anthonytec2/OctoSense/OctoSense/CAD/Mock Motherboard.SLDPRT

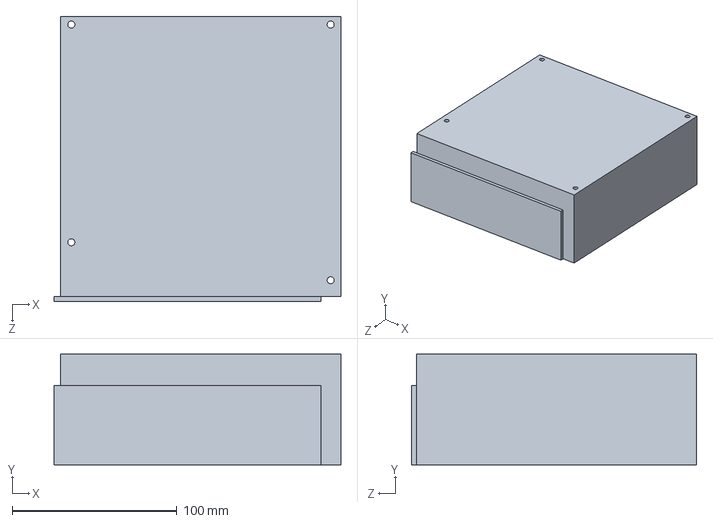
[picture p16: CAD file, 2026-06-25]
OctoSense/CAD/Mock Motherboard.SLDPRT
174.0 x 67.0 x 173.0 mm
