anthonytec2/OctoSense/OctoSense/CAD/Top Camera Case.SLDPRT

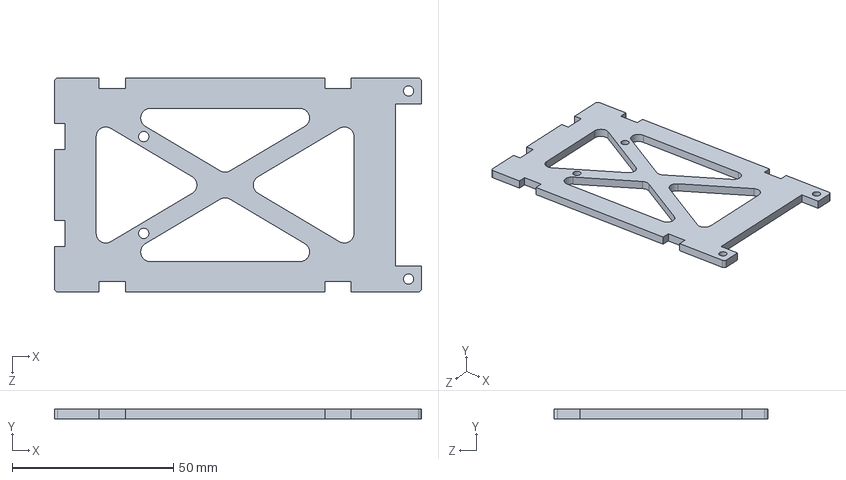
[picture p17: CAD file, 2026-06-25]
OctoSense/CAD/Top Camera Case.SLDPRT
113.8 x 3.17 x 66.3 mm
