anthonytec2/OctoSense/OctoSense/CAD/Mock Battery.SLDPRT

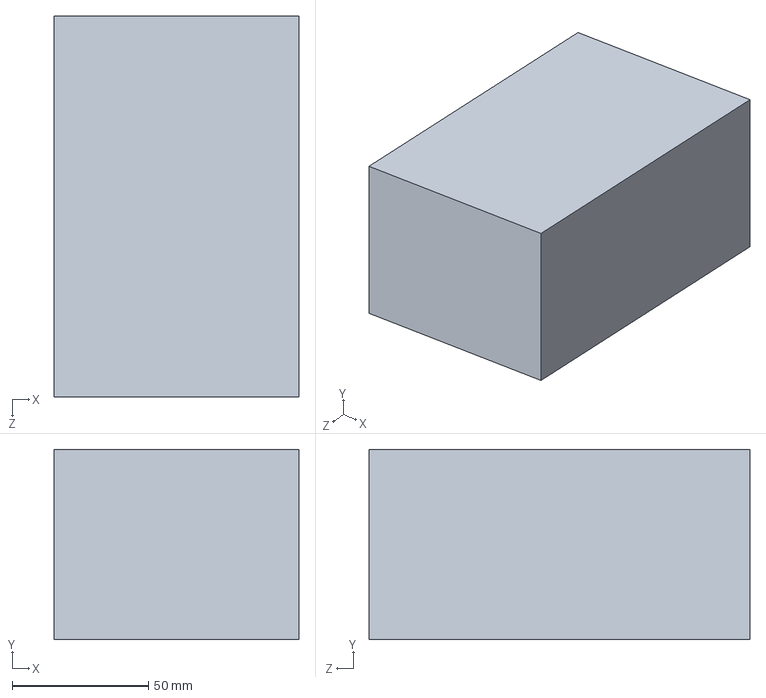
[picture p18: CAD file, 2026-06-25]
OctoSense/CAD/Mock Battery.SLDPRT
90.0 x 70.0 x 140.0 mm
