anthonytec2/OctoSense/OctoSense/CAD/Components Plate.SLDPRT

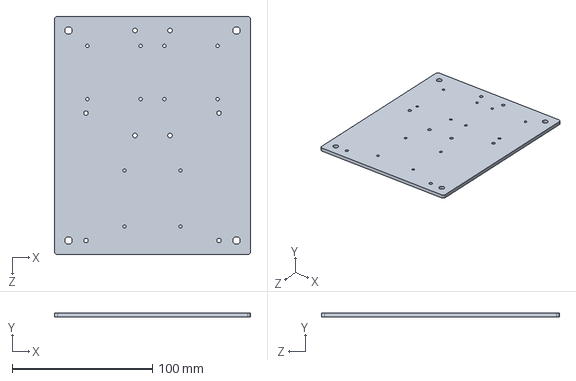
[picture p19: CAD file, 2026-06-25]
OctoSense/CAD/Components Plate.SLDPRT
140.0 x 3.17 x 170.0 mm
