anthonytec2/OctoSense/OctoSense/CAD/Car Mount.SLDPRT

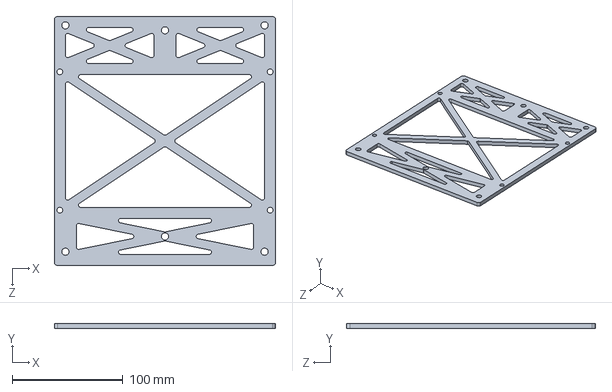
[picture p20: CAD file, 2026-06-25]
OctoSense/CAD/Car Mount.SLDPRT
200.0 x 4.76 x 225.0 mm
