anthonytec2/OctoSense/OctoSense/CAD/Mock Ouster Power.SLDPRT

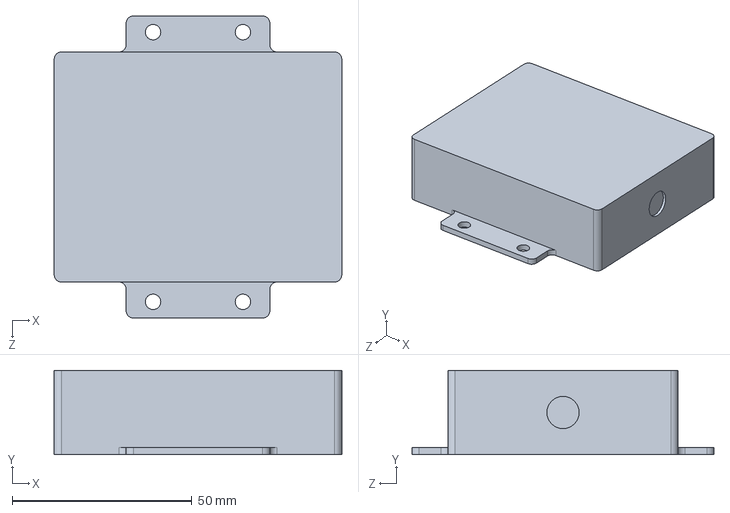
[picture p21: CAD file, 2026-06-25]
OctoSense/CAD/Mock Ouster Power.SLDPRT
80.0 x 23.5 x 84.0 mm
