anthonytec2/OctoSense/OctoSense/CAD/IMU Plate.SLDPRT

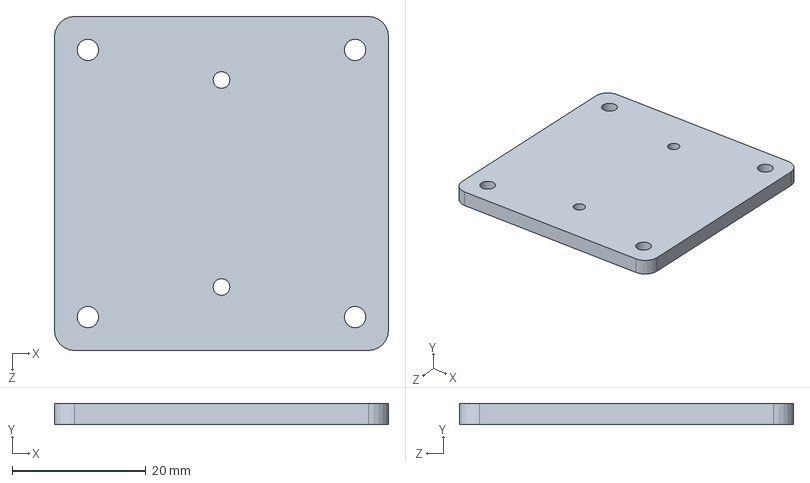
[picture p22: CAD file, 2026-06-25]
OctoSense/CAD/IMU Plate.SLDPRT
50.0 x 3.17 x 50.0 mm
