anthonytec2/OctoSense/OctoSense/CAD/Ouster Cable Clamp Jeremy.SLDPRT

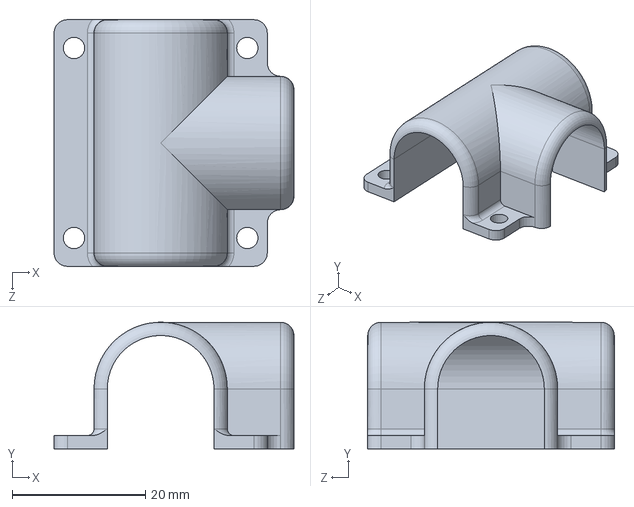
[picture p23: CAD file, 2026-06-25]
OctoSense/CAD/Ouster Cable Clamp Jeremy.SLDPRT
36.0 x 19.0 x 37.0 mm
