anthonytec2/OctoSense/OctoSense/CAD/Mock Ethernet Hub.SLDPRT

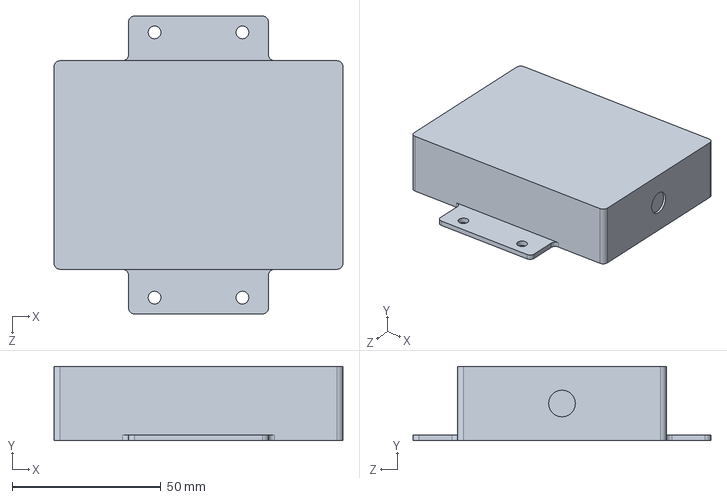
[picture p24: CAD file, 2026-06-25]
OctoSense/CAD/Mock Ethernet Hub.SLDPRT
97.0 x 25.0 x 100.0 mm
