anthonytec2/OctoSense/OctoSense/CAD/Mock Antenna.SLDPRT

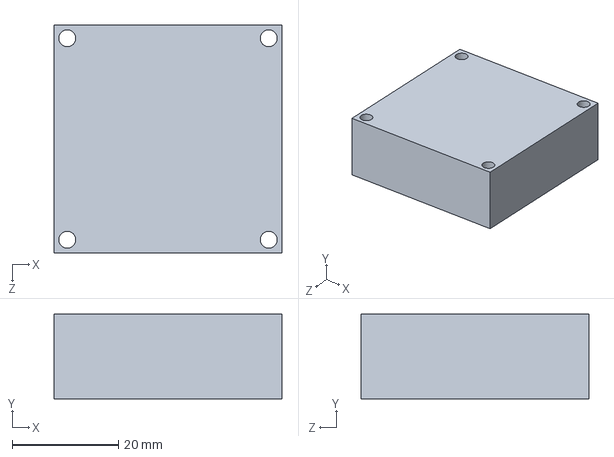
[picture p25: CAD file, 2026-06-25]
OctoSense/CAD/Mock Antenna.SLDPRT
43.0 x 16.0 x 43.0 mm
