anthonytec2/OctoSense/OctoSense/CAD/Mock Event Cameras.SLDPRT

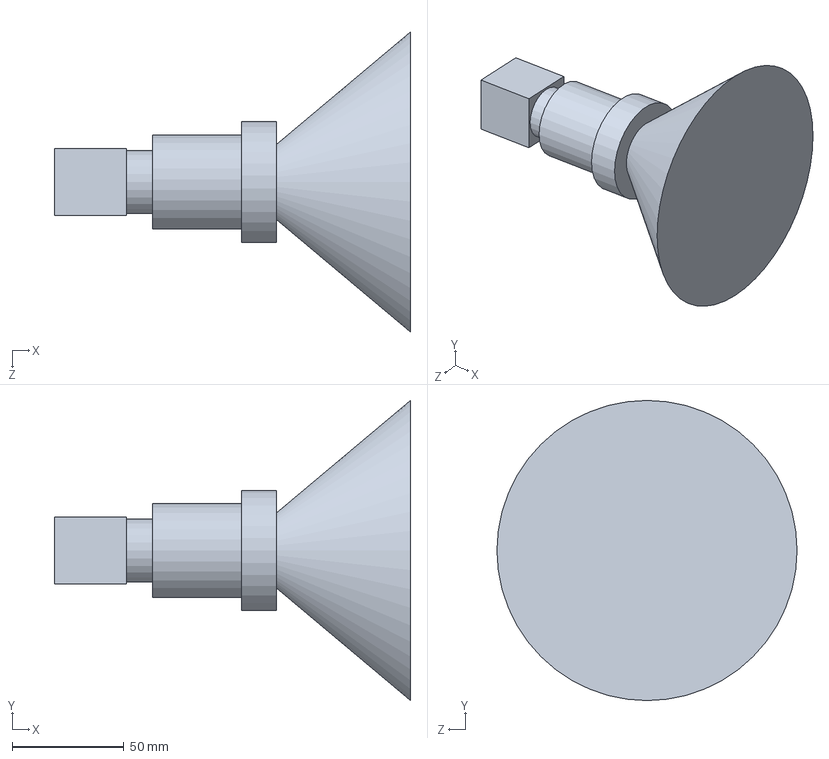
[picture p26: CAD file, 2026-06-25]
OctoSense/CAD/Mock Event Cameras.SLDPRT
159.2 x 134.3 x 134.3 mm
