anthonytec2/OctoSense/OctoSense/CAD/Ouster Heatsink Plate.SLDPRT

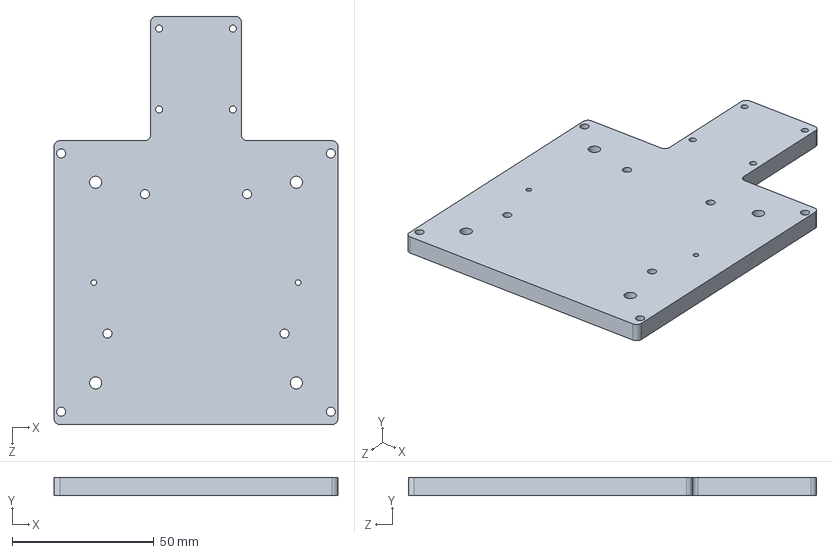
[picture p27: CAD file, 2026-06-25]
OctoSense/CAD/Ouster Heatsink Plate.SLDPRT
100.0 x 6.35 x 143.8 mm
