anthonytec2/OctoSense/OctoSense/CAD/Shelf.SLDPRT

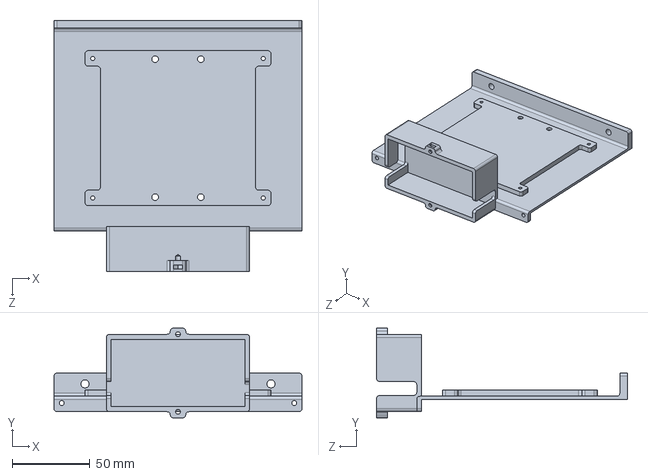
[picture p28: CAD file, 2026-06-25]
OctoSense/CAD/Shelf.SLDPRT
160.0 x 58.0 x 162.0 mm
