anthonytec2/OctoSense/OctoSense/CAD/Buck Converter Plate.SLDPRT

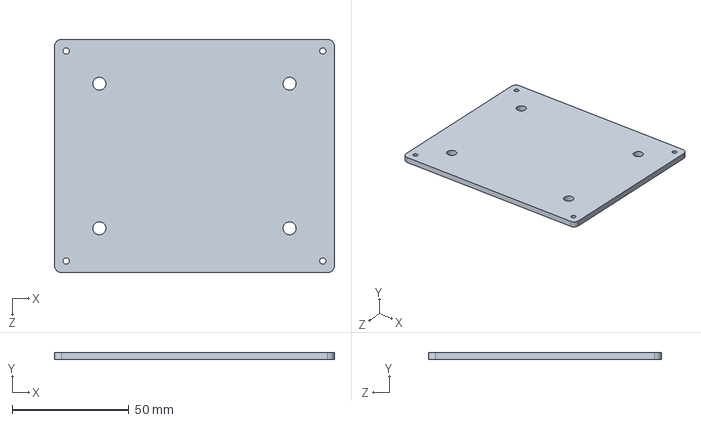
[picture p29: CAD file, 2026-06-25]
OctoSense/CAD/Buck Converter Plate.SLDPRT
120.0 x 3.17 x 100.0 mm
