anthonytec2/OctoSense/OctoSense/CAD/Camera Base.SLDPRT

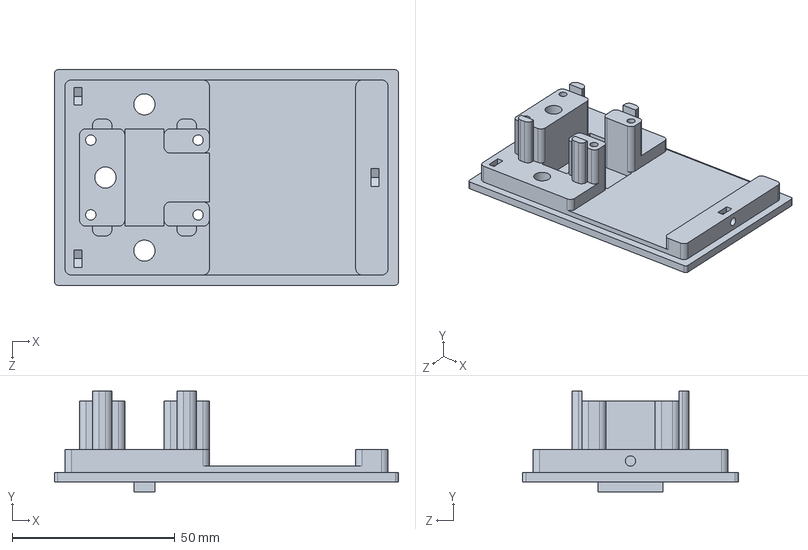
[picture p30: CAD file, 2026-06-25]
OctoSense/CAD/Camera Base.SLDPRT
105.8 x 31.0 x 66.3 mm
