anthonytec2/OctoSense/OctoSense/CAD/Mock IMU.SLDPRT

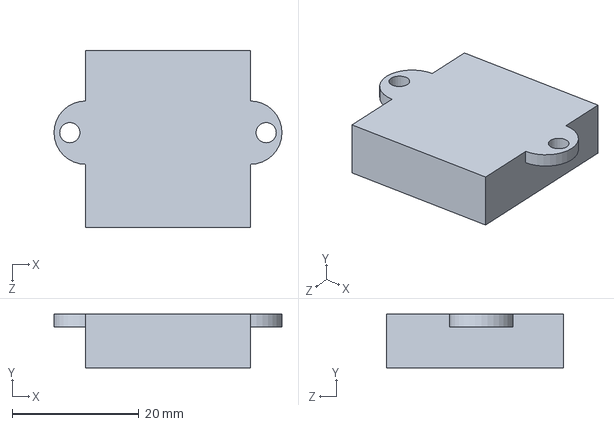
[picture p31: CAD file, 2026-06-25]
OctoSense/CAD/Mock IMU.SLDPRT
36.0 x 8.50 x 28.0 mm
