anthonytec2/OctoSense/OctoSense/CAD/Mock Power Distribution.SLDPRT

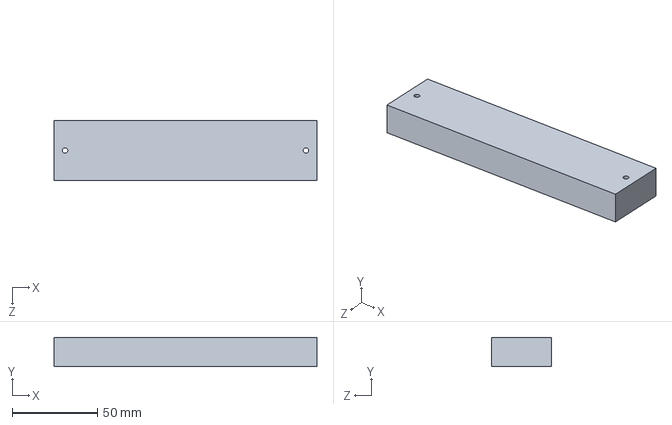
[picture p32: CAD file, 2026-06-25]
OctoSense/CAD/Mock Power Distribution.SLDPRT
154.0 x 17.0 x 35.0 mm
