anthonytec2/OctoSense/OctoSense/CAD/Sensor Suite Top Plate.SLDPRT

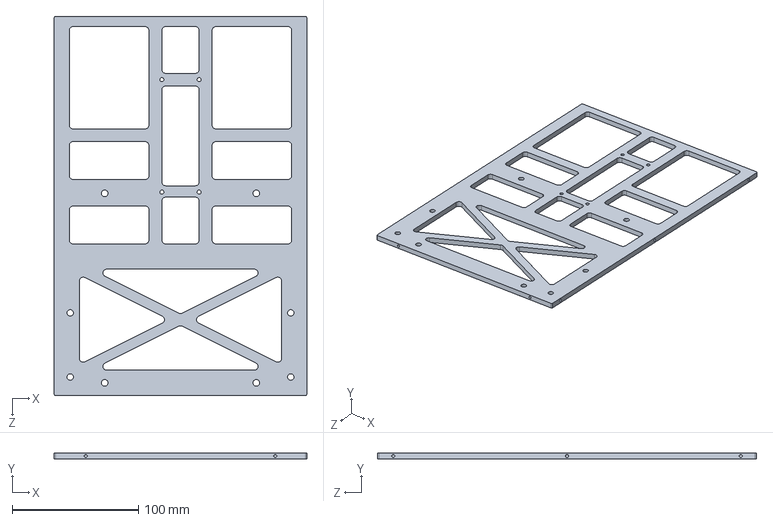
[picture p33: CAD file, 2026-06-25]
OctoSense/CAD/Sensor Suite Top Plate.SLDPRT
200.0 x 4.76 x 300.0 mm
