anthonytec2/OctoSense/OctoSense/CAD/Mock IR Filter.SLDPRT

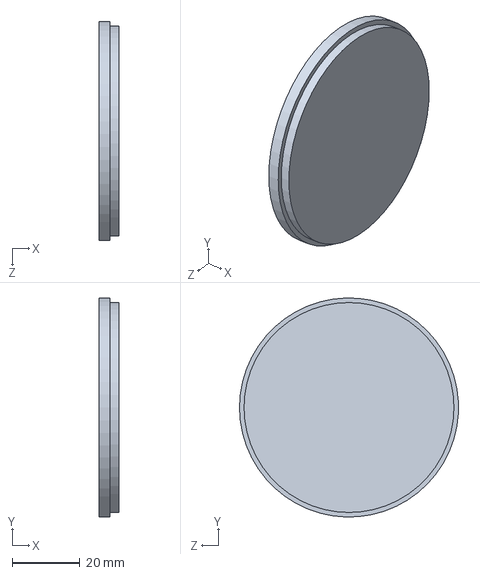
[picture p34: CAD file, 2026-06-25]
OctoSense/CAD/Mock IR Filter.SLDPRT
5.85 x 64.5 x 64.5 mm
