anthonytec2/OctoSense/OctoSense/CAD/Battery Case.SLDPRT

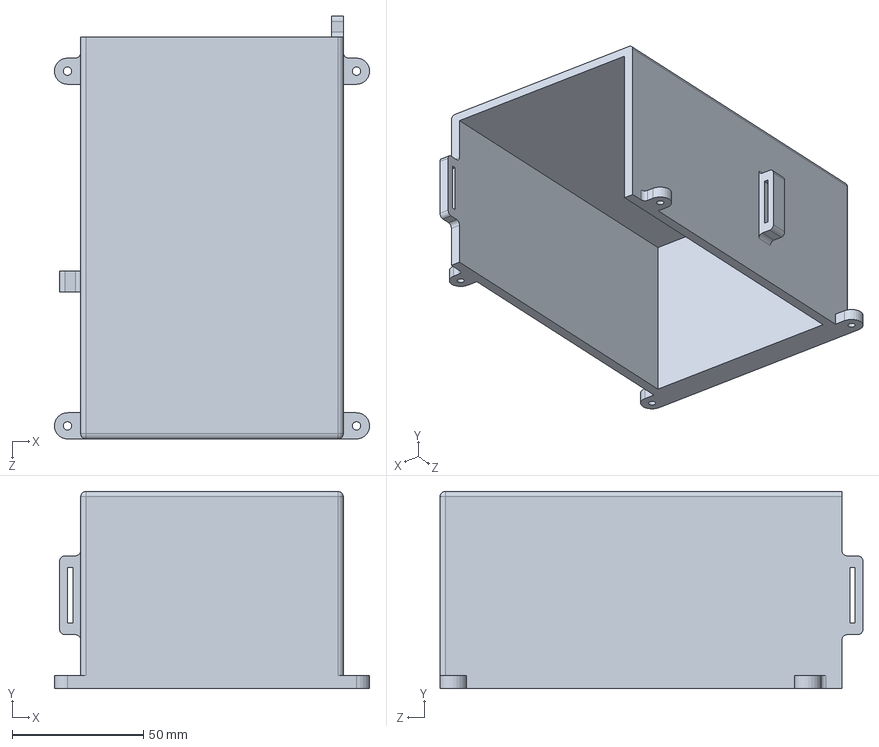
[picture p35: CAD file, 2026-06-25]
OctoSense/CAD/Battery Case.SLDPRT
120.0 x 75.0 x 161.0 mm
