anthonytec2/OctoSense/OctoSense/CAD/Left Side Sensor Tower Plate.SLDPRT

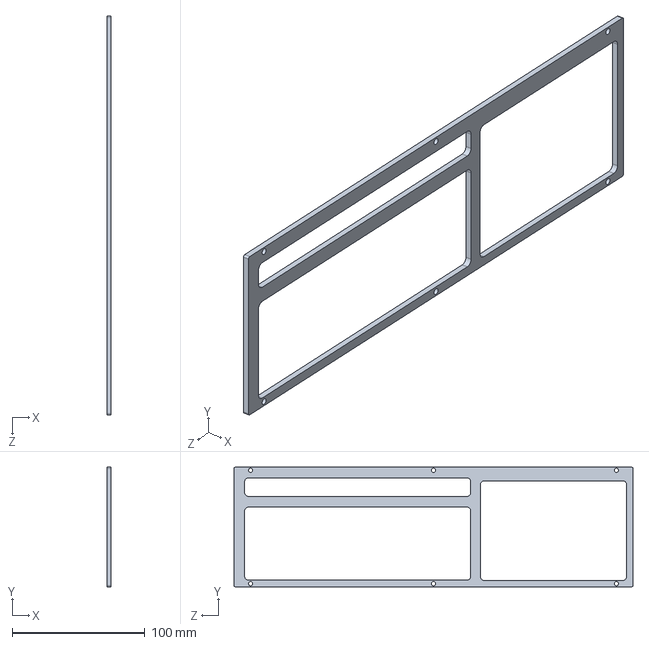
[picture p36: CAD file, 2026-06-25]
OctoSense/CAD/Left Side Sensor Tower Plate.SLDPRT
3.17 x 90.0 x 300.0 mm
