anthonytec2/OctoSense/OctoSense/CAD/Support Plates.SLDPRT

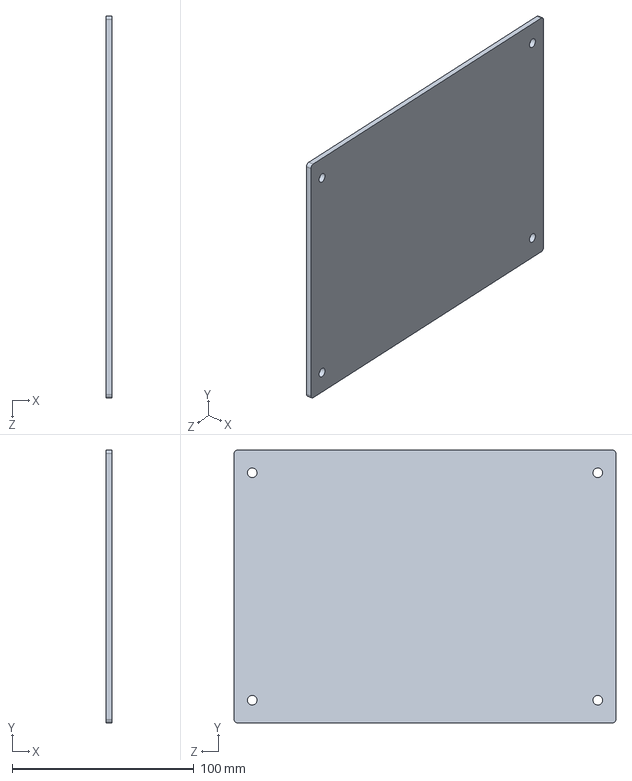
[picture p37: CAD file, 2026-06-25]
OctoSense/CAD/Support Plates.SLDPRT
3.17 x 150.0 x 210.0 mm
