anthonytec2/OctoSense/OctoSense/CAD/80-20 Camera Bar.SLDPRT

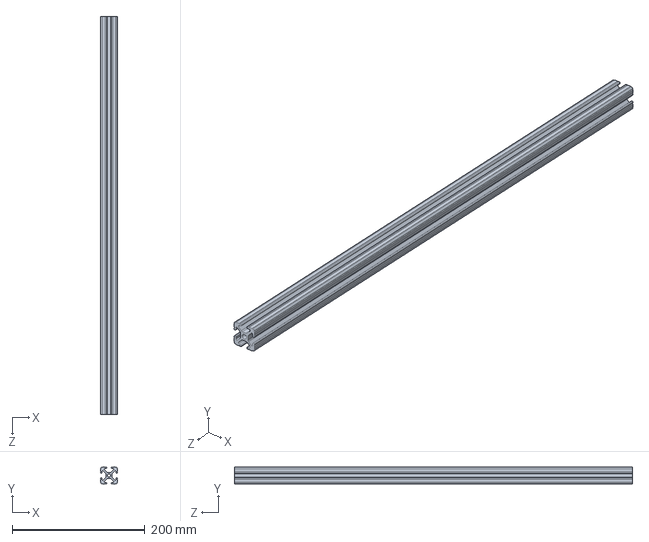
[picture p38: CAD file, 2026-06-25]
OctoSense/CAD/80-20 Camera Bar.SLDPRT
25.4 x 25.4 x 600.0 mm
