anthonytec2/OctoSense/OctoSense/CAD/Thermal Camera Base.SLDPRT

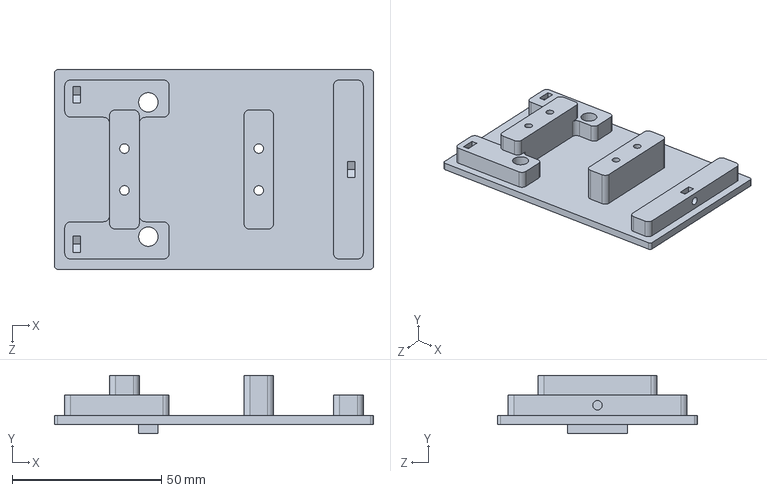
[picture p39: CAD file, 2026-06-25]
OctoSense/CAD/Thermal Camera Base.SLDPRT
106.8 x 19.5 x 66.8 mm
