anthonytec2/OctoSense/OctoSense/CAD/Back Camera Case.SLDPRT

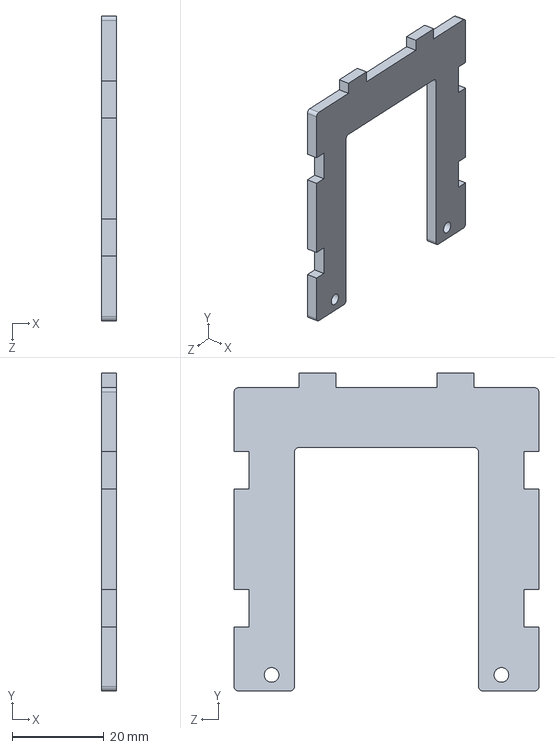
[picture p40: CAD file, 2026-06-25]
OctoSense/CAD/Back Camera Case.SLDPRT
3.17 x 69.2 x 66.3 mm
