anthonytec2/OctoSense/OctoSense/CAD/Cage Mount V2.SLDPRT

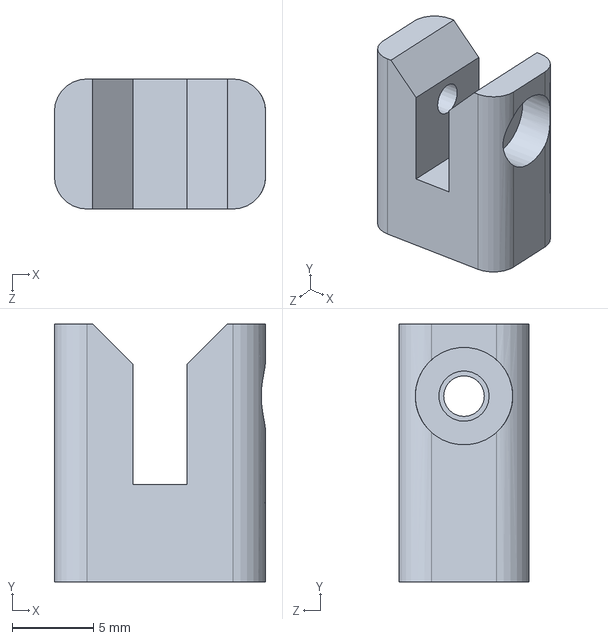
[picture p41: CAD file, 2026-06-25]
OctoSense/CAD/Cage Mount V2.SLDPRT
13.0 x 15.9 x 8.00 mm
