anthonytec2/OctoSense/OctoSense/CAD/Camera Stack.SLDASM

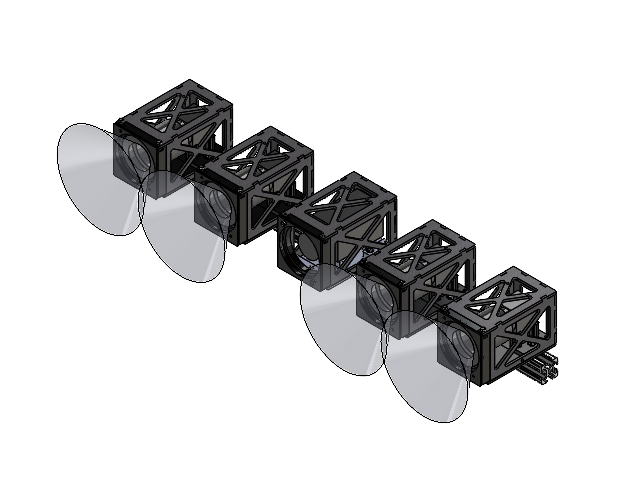
[picture p44: CAD file, 2026-06-25]
OctoSense/CAD/Camera Stack.SLDASM
80-20 Camera Bar
Camera Base x 4
Side Camera Case x 10
Back Camera Case x 5
Top Camera Case x 5
Camera Front Case Plate x 5
IR Filter Clamp x 5
91290A228_Black-Oxide Alloy Steel Socket Head Screw x 10
M3 91290A115_Black-Oxide Alloy Steel Socket Head Screw x 20
Mock Event Cameras x 4
Thermal Camera Base
Mock Thermal Camera
