anthonytec2/OctoSense/OctoSense/CAD/Event Camera Case.SLDASM

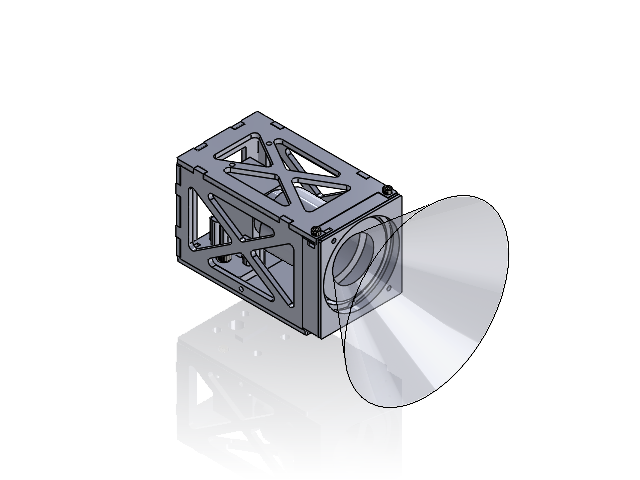
[picture p45: CAD file, 2026-06-25]
OctoSense/CAD/Event Camera Case.SLDASM
Camera Base
Side Camera Case x 2
Back Camera Case
Top Camera Case
Mock Event Cameras
Camera Front Case Plate
IR Filter Clamp
91290A228_Black-Oxide Alloy Steel Socket Head Screw x 2
M3 91290A115_Black-Oxide Alloy Steel Socket Head Screw x 4
